VladimirPokorny/Remote-thermometer-nRF52/Hardware Files/Schematic Layout PDF files/3D render/PCB_3D_Print.png

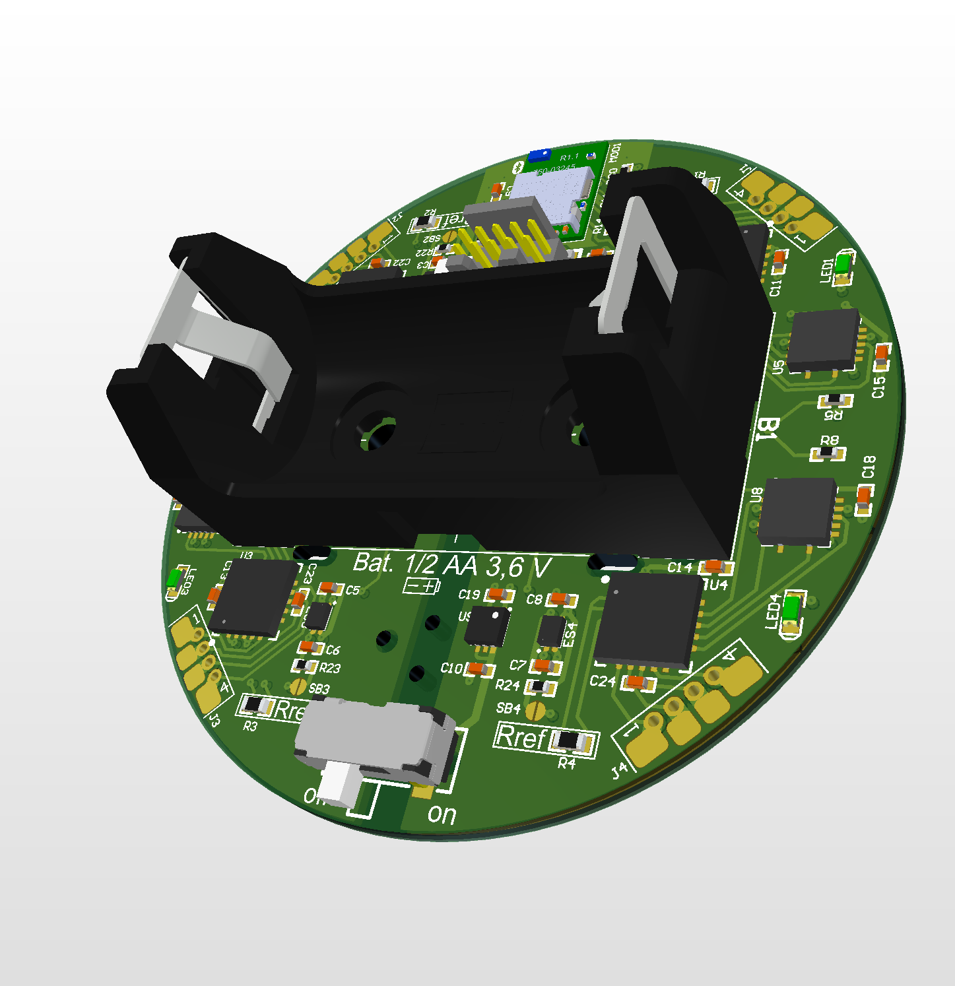
Hardware Files/Schematic Layout PDF files/3D render/PCB_3D_Print.png
